Nolno/PFE_CasqueVelo/3D/Piece_Guidon/Corps4.stl

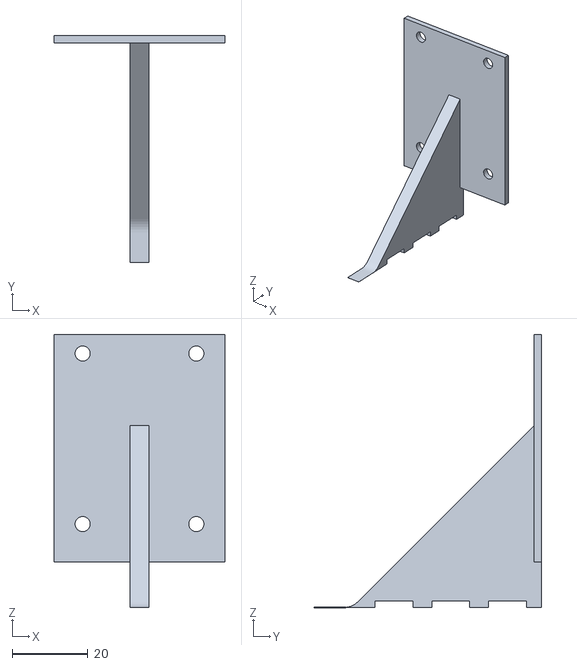
[picture p21: CAD file, 2025-02-14]
3D/Piece_Guidon/Corps4.stl
45.0 x 60.0 x 72.0
