Nolno/PFE_CasqueVelo/3D/banc_test/support_carte.stl

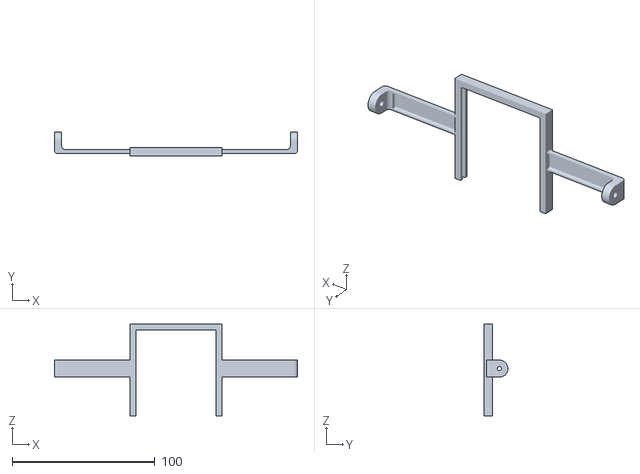
[picture p22: CAD file, 2025-01-24]
3D/banc_test/support_carte.stl
170.0 x 16.7 x 64.1
