Nolno/PFE_CasqueVelo/3D/Piece_Guidon/Piece Vélo entier.stl

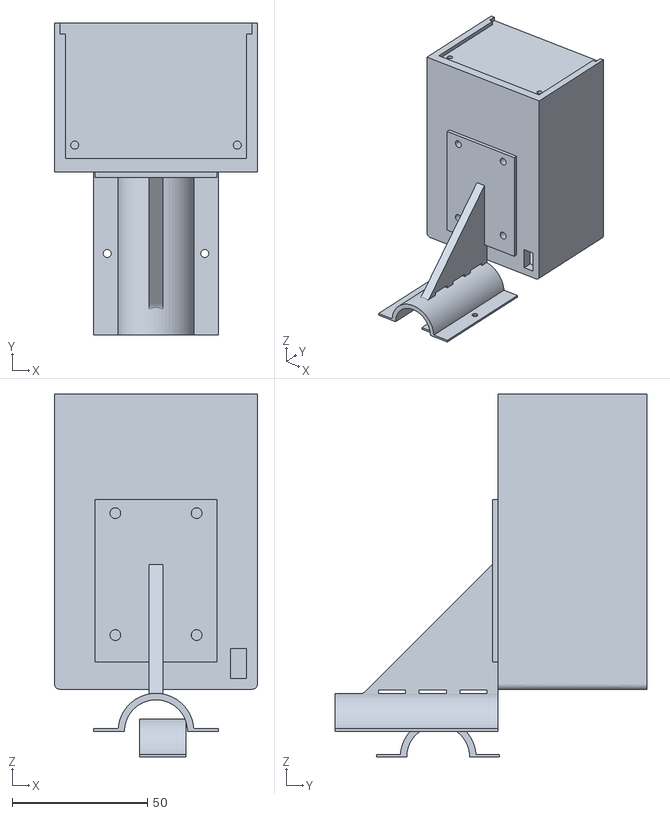
[picture p23: CAD file, 2025-02-07]
3D/Piece_Guidon/Piece Vélo entier.stl
75.0 x 115.0 x 134.0
