Nolno/PFE_CasqueVelo/3D/banc_test/Corps de maillage1.stl

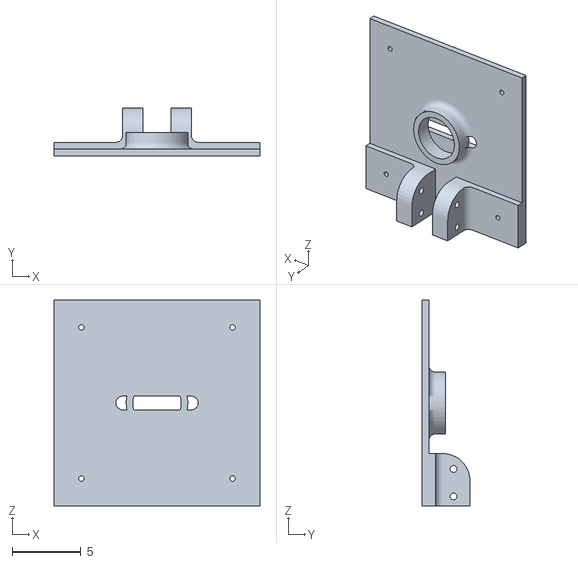
[picture p24: CAD file, 2025-01-24]
3D/banc_test/Corps de maillage1.stl
15.0 x 3.50 x 15.0
