Nolno/PFE_CasqueVelo/3D/banc_test/vertical_support_part_bottom.stl

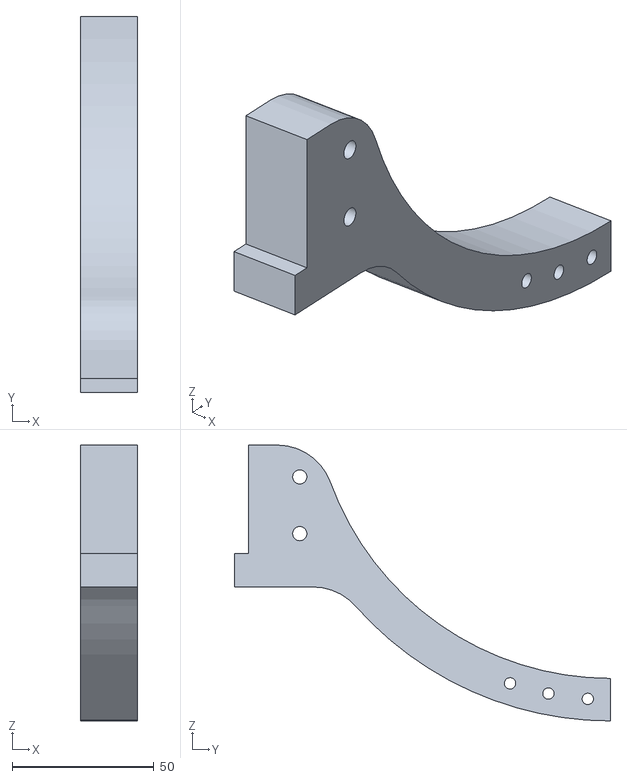
[picture p25: CAD file, 2025-01-24]
3D/banc_test/vertical_support_part_bottom.stl
20.0 x 132.5 x 97.2
