Nolno/PFE_CasqueVelo/3D/banc_test/ring_2_quater_X3.stl

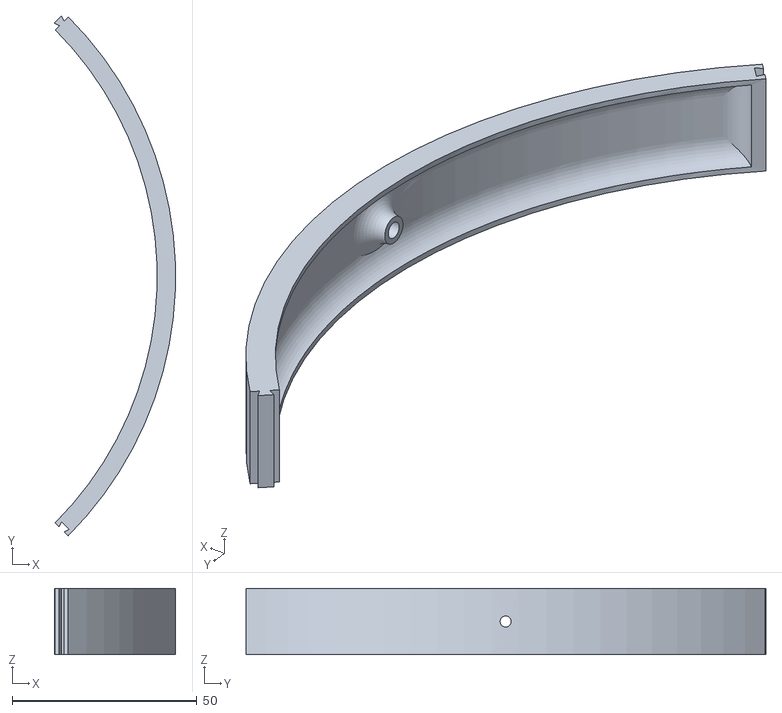
[picture p26: CAD file, 2025-01-24]
3D/banc_test/ring_2_quater_X3.stl
32.9 x 140.9 x 18.0
