Nolno/PFE_CasqueVelo/src/MPU.h

/**
* @file MPU.h
 * @author Antoine Martin
 * @brief Code de gestion du MPU. Ce code fonctionne sur un ESP32-WROOM-32E avec un IMU ICM20948 de chez Adafruit.
 * @version 1.0
 * @date 25/02/2024
 *
 * @copyright Copyright (c) 2025
 *
 */
#ifndef MPU_H
#define MPU_H
#define BUFFER_SIZE 25 /**< Taille du buffer pour la moyenne des angles d'orientation */

#include <Arduino.h>
#include <Adafruit_ICM20948.h>
/**
* @brief Classe de gestion du MPU. La classe permet de récupérer les angles d'orientation du MPU(yaw, pitch, roll).
* L'initialisation et le calibrage du MPU et du DMP est effectué dans la classe, ainsi que les éventuels traitements des données.
*/
class MPU {
private:
    Adafruit_ICM20948 icm; /**< Objet pour la gestion du MPU */
    // Angles d'orientation
    float ypr[3]; /**< Tableau pour stocker les valeurs des angles d'orientation [yaw, pitch, roll] */
    float yawBuffer[BUFFER_SIZE]; /**< Buffer pour stocker les valeurs de l'angle de lacet */
    float pitchBuffer[BUFFER_SIZE]; /**< Buffer pour stocker les valeurs de l'angle de tangage */
    float rollBuffer[BUFFER_SIZE]; /**< Buffer pour stocker les valeurs de l'angle de roulis */
    int bufferIndex;  /**< Index actuel dans le buffer */
    bool bufferFull;  /**< Indique si on a rempli au moins x valeurs */

    // Variables pour la calibration
    unsigned long startTime; /**< Temps de démarrage de la calibration */
    // Variables de calibration
    float magMinX = 1000, magMaxX = -1000; // Valeurs min et max pour l'axe X
    float magMinY = 1000, magMaxY = -1000; // Valeurs min et max pour l'axe Y
    float magMinZ = 1000, magMaxZ = -1000; // Valeurs min et max pour l'axe Z

    float magOffsetX = 0, magOffsetY = 0, magOffsetZ = 0; // Offset pour chaque axe
    float magScaleX = 1, magScaleY = 1, magScaleZ = 1; // Facteur d'échelle pour chaque axe

    // Variables pour le Filtre de Kalman
    float kalmanYaw = 0;  // Estimation du Yaw
    float kalmanError = 4; // Erreur estimée initiale
    float kalmanGain = 0.5;  // Gain de Kalman
    float sensorError = 2; // Bruit de mesure (ajuste si nécessaire)
    float kalmanX = 0;
    float kalmanY = 0;

    float correctionFactor=0.5; // Facteur de correction pour la moyenne

    unsigned long temps; /**< Temps actuel en millisecondes */


    /**
    * @brief Méthode pour ajouter un échantillon dans le buffer utilisé pour le calcul de la moyenne.
    */
    void addSample(float new_yaw, float new_pitch, float new_roll);
    /**
     * @brief Applique un filtre de Kalman sur la mesure de l'angle de lacet.
     * @param measured_yaw Valeur mesurée de l'angle de lacet.
     * @return
     */
    float applyKalmanFilter(float measured_yaw);
    /**
     * @brief Calcule la différence entre deux angles. La différence est calculée en tenant compte de la périodicité de 360°.
     * @param a Premier angle.
     * @param b Deuxième angle.
     * @return Différence entre les deux angles.
     */
    static float getAngleDifference(float a, float b);
public:
    /**
    * @brief Constructeur de la classe MPU.
    */
    explicit MPU();

    /**
    * @brief Méthode pour initialiser le MPU. Cette méthode doit être appelée une seule fois au démarrage du programme.
    */
    void initialize();

    /**
    * @brief Routine de mise à jour du MPU. Appeler cette méthode régulièrement dans la boucle principale (loop).
    */
    void update();

    /**
    * @brief Méthode pour récupérer la valeur de l'angle de lacet.
    */
    float getYaw() const;

    /**
    * @brief Méthode pour récupérer la valeur de l'angle de tangage.
    */
    float getPitch() const;

    /**
    * @brief Méthode pour récupérer la valeur de l'angle de roulis.
    */
    float getRoll() const;

    /**
    * @brief Méthode pour récupérer les valeurs des angles d'orientation (yaw, pitch, roll) en degrés.
    */
    void getYPR(float (&ypr)[3]) const;

    /**
    * @brief Méthode pour obtenir les valeurs moyennes des angles d'orientation en degrés.
    * @param avg_yaw Valeur moyenne de l'angle de lacet.
    * @param avg_pitch Valeur moyenne de l'angle de tangage.
    * @param avg_roll Valeur moyenne de l'angle de roulis.
    */
    void getAveragedYPR(float &avg_yaw, float &avg_pitch, float &avg_roll) const;

    /**
     * @brief Méthode pour obtenir les valeurs moyennes des angles d'orientation en degrés.
     * @param ypr Tableau contenant les valeurs des angles d'orientation [yaw, pitch, roll]
     */
    void getAveragedYPR(float (&ypr)[3]) const;
};

#endif //MPU_H
